SNL-WaterPower/siweed/documentation/diagrams/NoiseHistogram.pdf

-6 | -4 | -2 | 0 | 2 | 4 | 6 | 8
Torque Measured(N-m) | #10⁻⁵

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
Occurences
