SNL-WaterPower/siweed/documentation/diagrams/siweed_photo_with_callouts.pdf

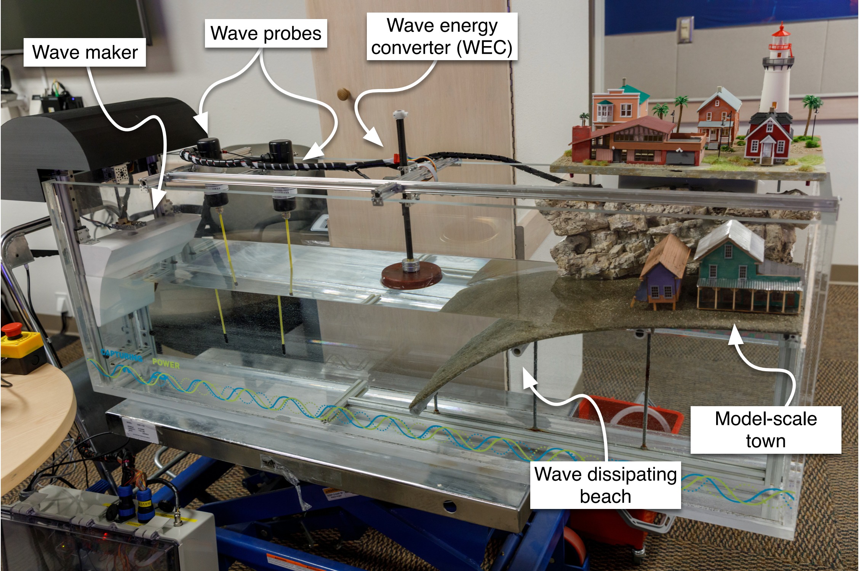
[picture p4: page 1]

Wave probes
Wave maker

Wave energy
converter (WEC)

Wave dissipating
beach

Model-scale
town
