SNL-WaterPower/siweed/Processing/siWeedGUI/1.png

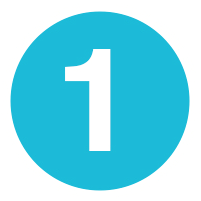
Processing/siWeedGUI/1.png
