SNL-WaterPower/siweed/Processing/siWeedGUI/2.png

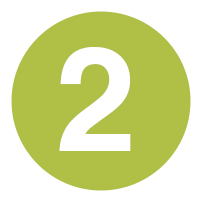
Processing/siWeedGUI/2.png
