SNL-WaterPower/siweed/documentation/SOLIDWORKS Town/Wave Maker (all parts)/FinalWaveMaker.SLDPRT

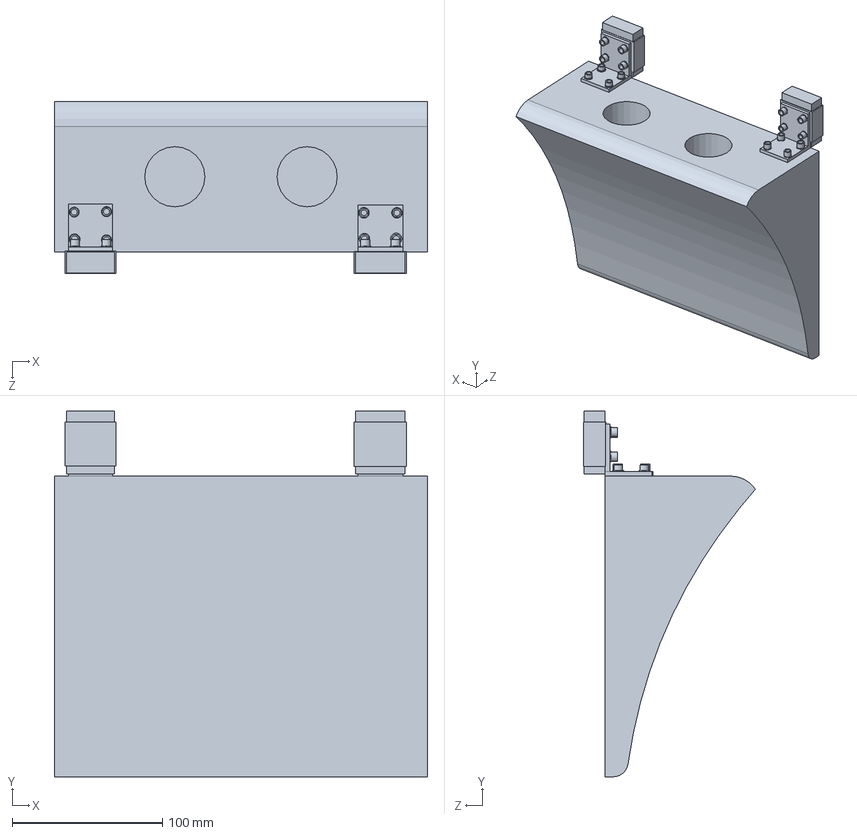
[picture p28: CAD file, 2022-12-22]
documentation/SOLIDWORKS Town/Wave Maker (all parts)/FinalWaveMaker.SLDPRT
248.0 x 243.1 x 114.3 mm
