SNL-WaterPower/siweed/documentation/SOLIDWORKS Town/Buoy (all prts)/Final buoy.SLDPRT

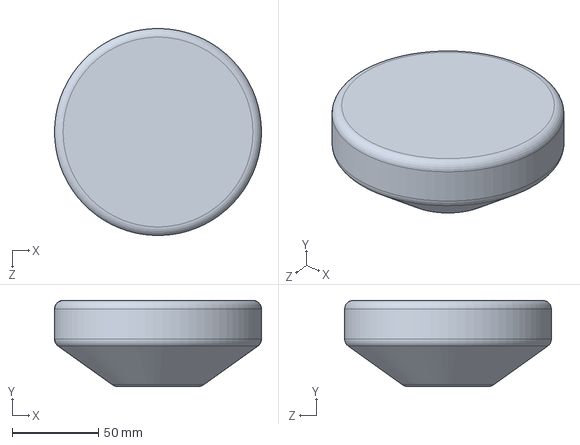
[picture p29: CAD file, 2022-12-22]
documentation/SOLIDWORKS Town/Buoy (all prts)/Final buoy.SLDPRT
120.0 x 50.0 x 119.9 mm
