SNL-WaterPower/siweed/documentation/SOLIDWORKS Town/Buildings/Beginner House.SLDPRT

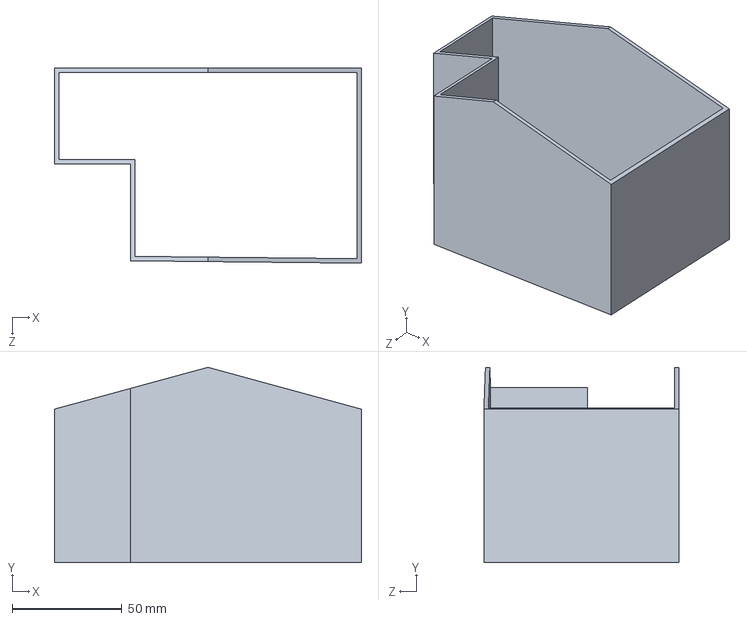
[picture p30: CAD file, 2022-12-22]
documentation/SOLIDWORKS Town/Buildings/Beginner House.SLDPRT
139.7 x 88.9 x 88.9 mm
