SNL-WaterPower/siweed/documentation/SOLIDWORKS Town/Buoy (all prts)/buoy.SLDPRT

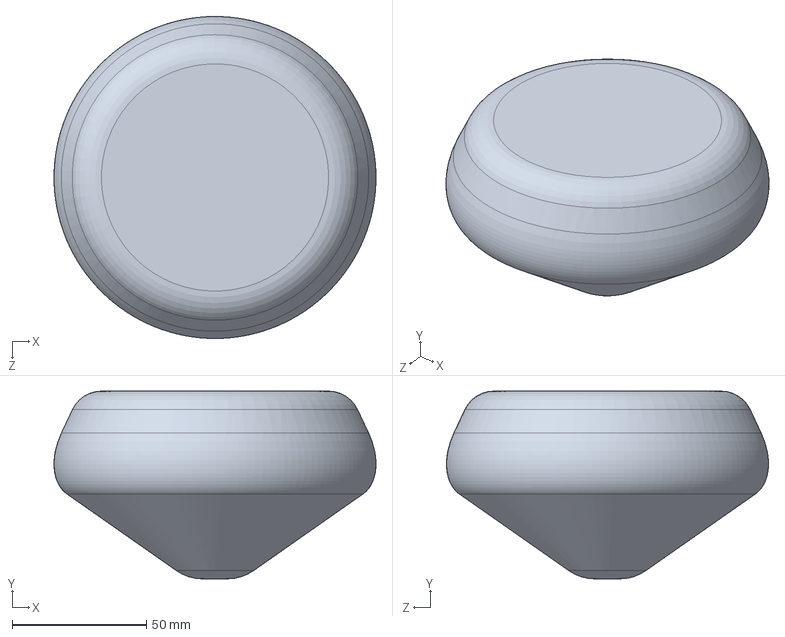
[picture p31: CAD file, 2022-12-22]
documentation/SOLIDWORKS Town/Buoy (all prts)/buoy.SLDPRT
120.0 x 70.0 x 120.0 mm
