SNL-WaterPower/siweed/documentation/SOLIDWORKS Town/Wave Maker (all parts)/Top Rods.SLDPRT

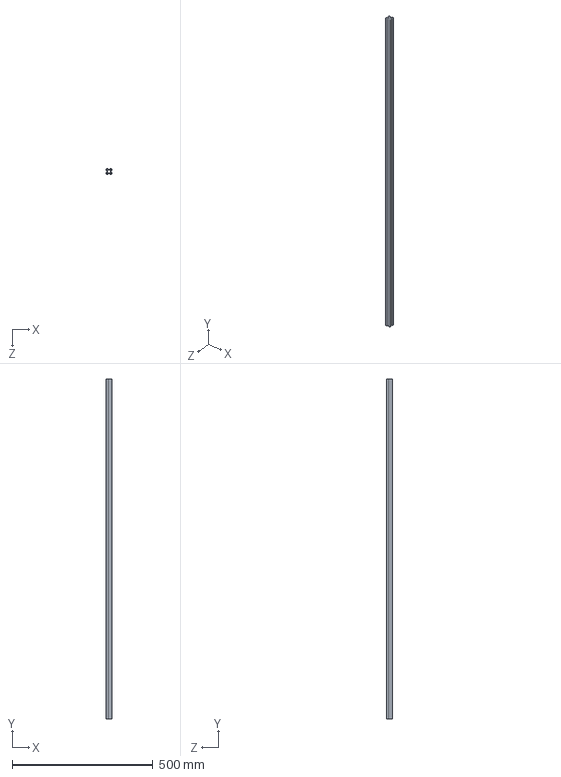
[picture p32: CAD file, 2022-12-22]
documentation/SOLIDWORKS Town/Wave Maker (all parts)/Top Rods.SLDPRT
20.1 x 1208.0 x 20.1 mm
