SNL-WaterPower/siweed/documentation/SOLIDWORKS Town/Buildings/light house.SLDPRT

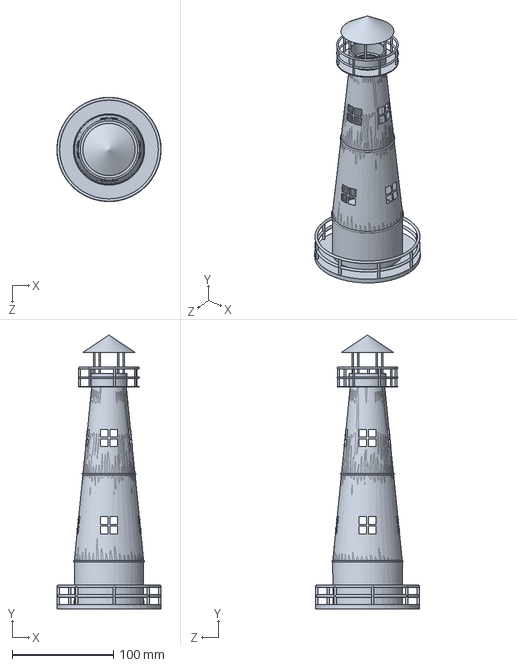
[picture p33: CAD file, 2022-12-22]
documentation/SOLIDWORKS Town/Buildings/light house.SLDPRT
103.0 x 270.3 x 103.0 mm
