SNL-WaterPower/siweed/documentation/SOLIDWORKS Town/Buoy (all prts)/Encoder.SLDPRT

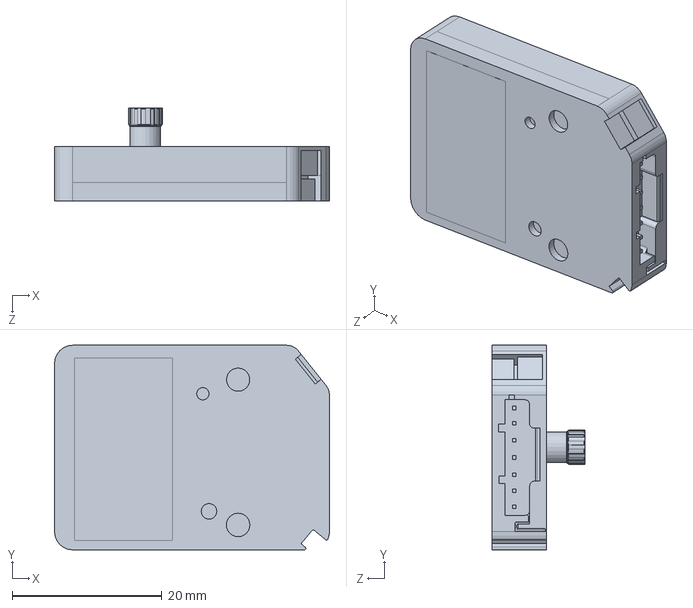
[picture p34: CAD file, 2022-12-22]
documentation/SOLIDWORKS Town/Buoy (all prts)/Encoder.SLDPRT
36.8 x 27.4 x 12.5 mm
