SNL-WaterPower/siweed/documentation/SOLIDWORKS Town/Wave Maker (all parts)/double S Top Rods -  - Copy.SLDPRT

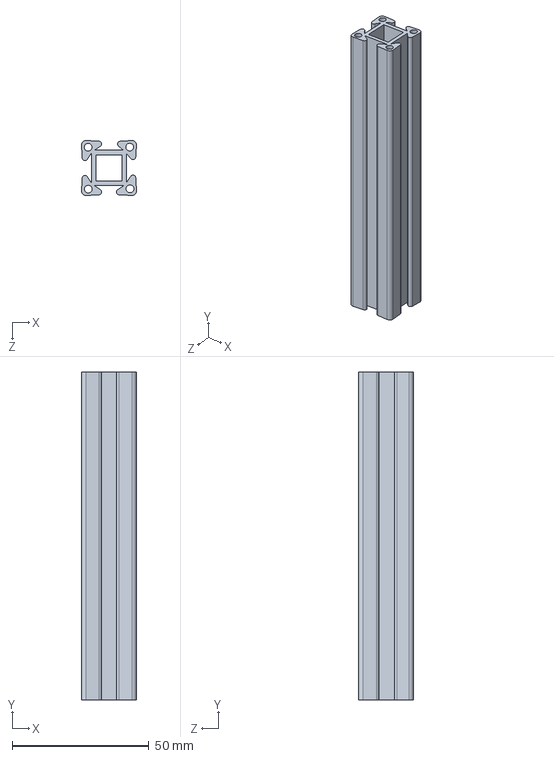
[picture p35: CAD file, 2022-12-22]
documentation/SOLIDWORKS Town/Wave Maker (all parts)/double S Top Rods - - Copy.SLDPRT
20.1 x 120.0 x 20.1 mm
