SNL-WaterPower/siweed/documentation/SOLIDWORKS Town/Buildings/beach shack.SLDPRT

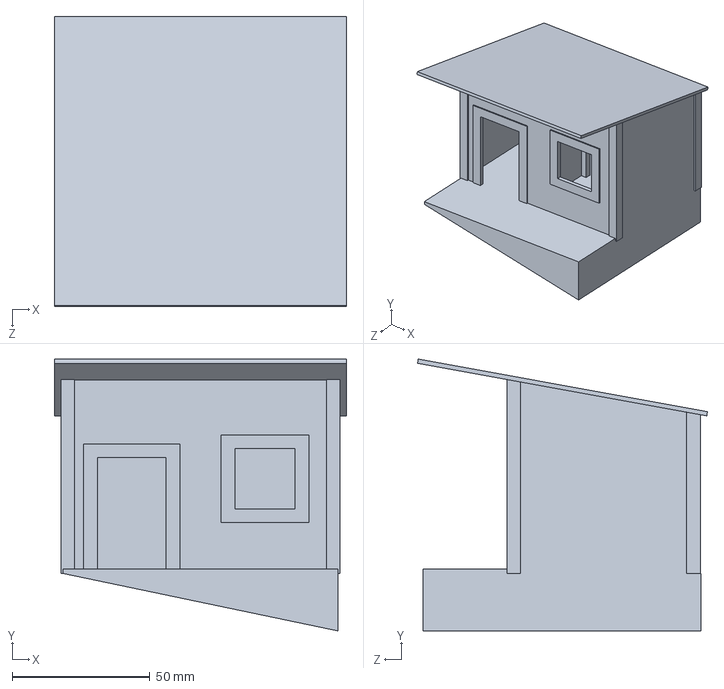
[picture p36: CAD file, 2022-12-22]
documentation/SOLIDWORKS Town/Buildings/beach shack.SLDPRT
106.2 x 98.8 x 105.4 mm
