SNL-WaterPower/siweed/documentation/SOLIDWORKS Town/Wave Maker (all parts)/mini bracket.SLDPRT

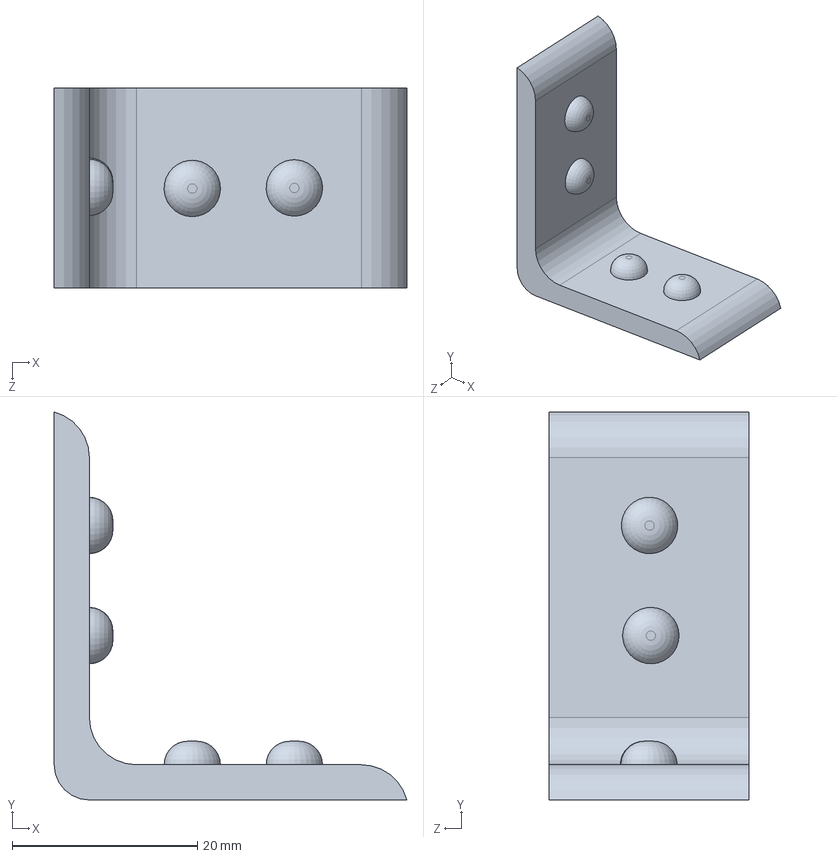
[picture p37: CAD file, 2022-12-22]
documentation/SOLIDWORKS Town/Wave Maker (all parts)/mini bracket.SLDPRT
38.1 x 41.9 x 21.6 mm
