SNL-WaterPower/siweed/documentation/SOLIDWORKS Town/Buildings/House.SLDPRT

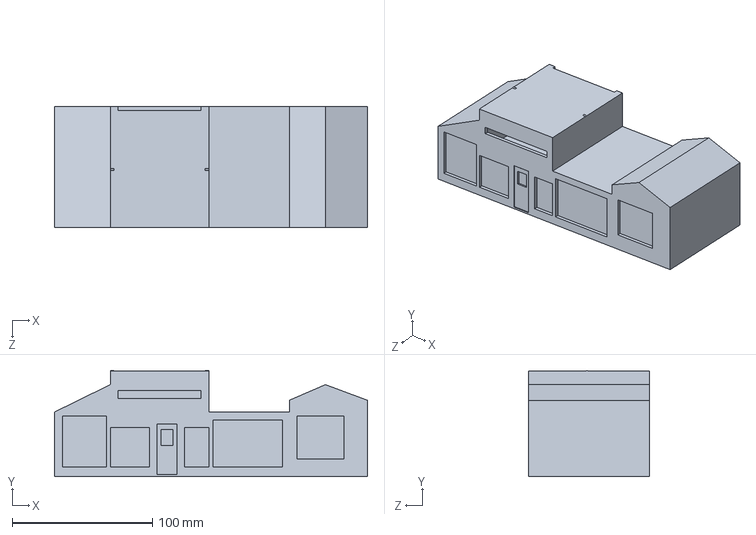
[picture p38: CAD file, 2022-12-22]
documentation/SOLIDWORKS Town/Buildings/House.SLDPRT
223.5 x 75.8 x 86.1 mm
