SNL-WaterPower/siweed/documentation/SOLIDWORKS Town/Wave Maker (all parts)/Horiz Rod.SLDPRT

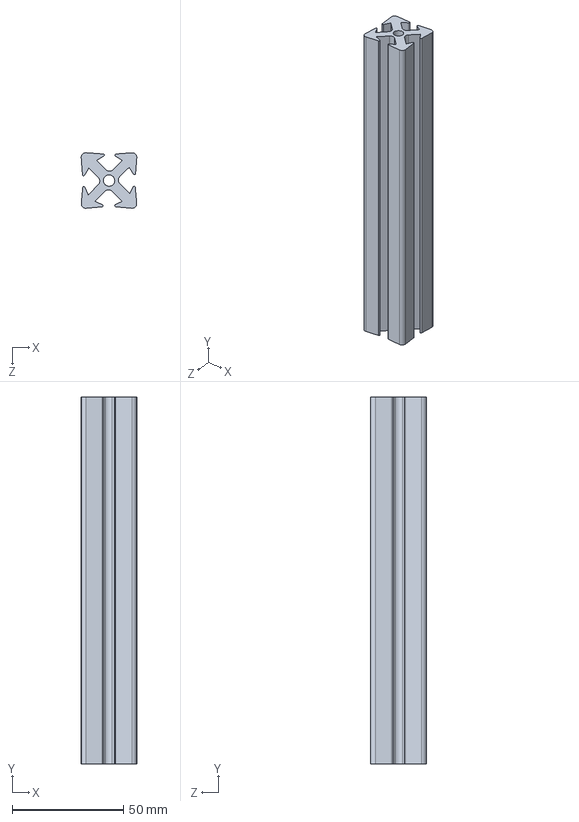
[picture p39: CAD file, 2022-12-22]
documentation/SOLIDWORKS Town/Wave Maker (all parts)/Horiz Rod.SLDPRT
25.0 x 165.2 x 25.0 mm
