SNL-WaterPower/siweed/documentation/SOLIDWORKS Town/Buoy (all prts)/bracket.SLDPRT

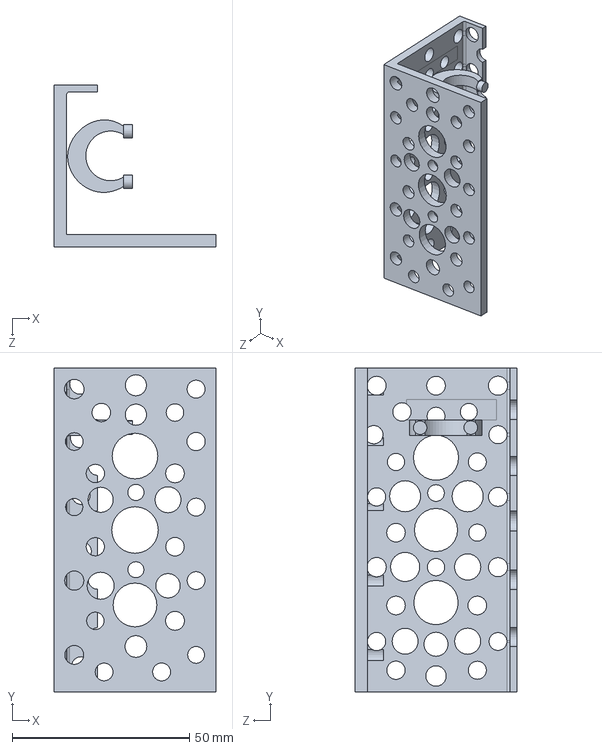
[picture p40: CAD file, 2022-12-22]
documentation/SOLIDWORKS Town/Buoy (all prts)/bracket.SLDPRT
45.7 x 91.4 x 45.7 mm
