SNL-WaterPower/siweed/documentation/SOLIDWORKS Town/Wave Maker (all parts)/Pulley.SLDPRT

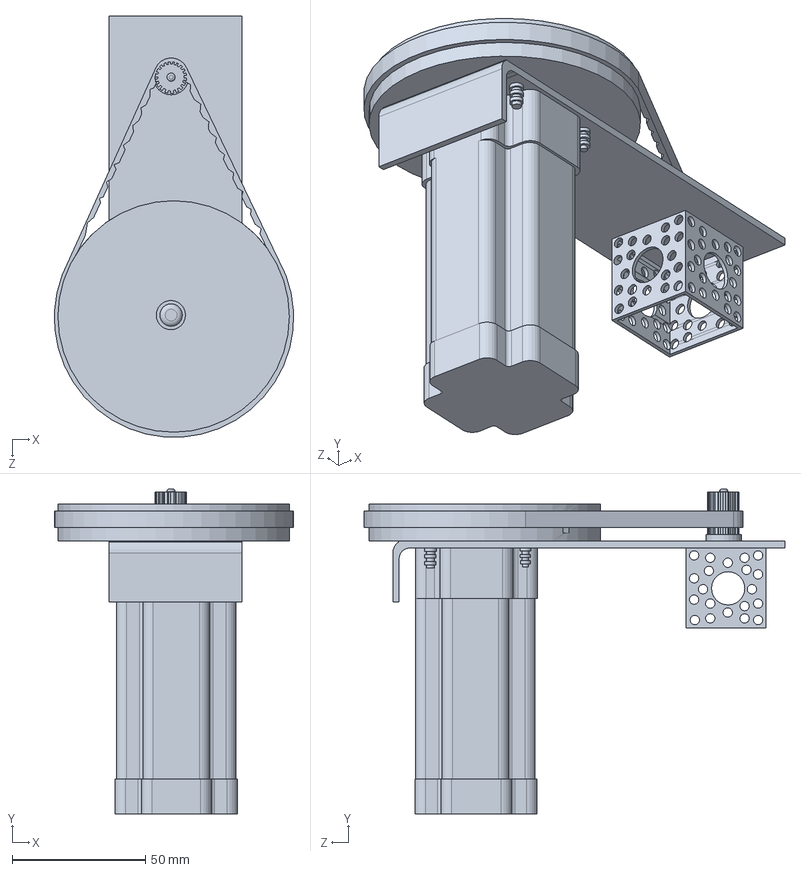
[picture p41: CAD file, 2022-12-22]
documentation/SOLIDWORKS Town/Wave Maker (all parts)/Pulley.SLDPRT
89.9 x 122.2 x 158.3 mm
