SNL-WaterPower/siweed/documentation/SOLIDWORKS Town/Buoy (all prts)/Motor.SLDPRT

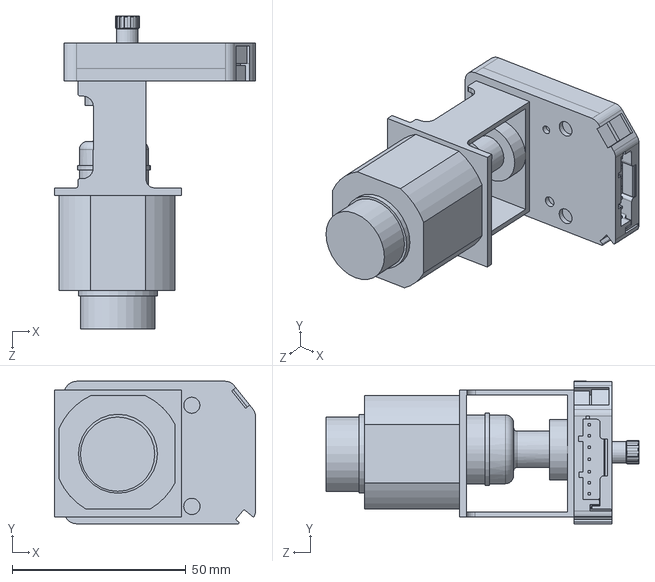
[picture p42: CAD file, 2022-12-22]
documentation/SOLIDWORKS Town/Buoy (all prts)/Motor.SLDPRT
57.9 x 41.1 x 90.0 mm
