SNL-WaterPower/siweed/documentation/SOLIDWORKS Town/Wave Maker (all parts)/Rod.SLDPRT

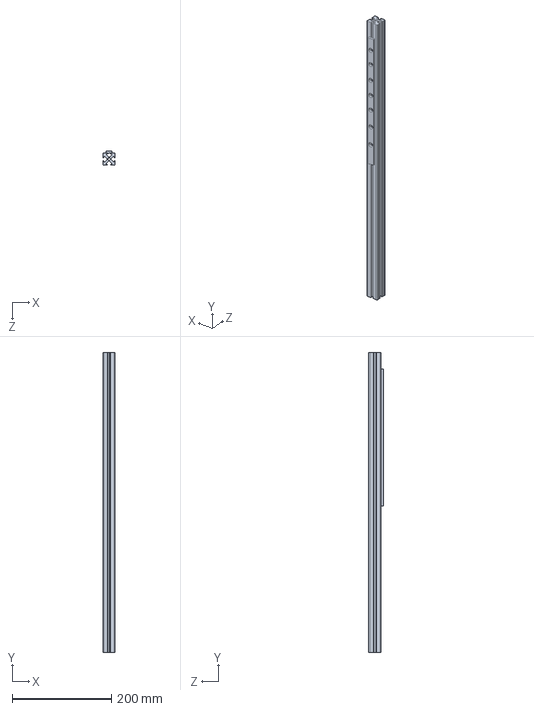
[picture p43: CAD file, 2022-12-22]
documentation/SOLIDWORKS Town/Wave Maker (all parts)/Rod.SLDPRT
25.0 x 603.2 x 29.3 mm
