SNL-WaterPower/siweed/documentation/SOLIDWORKS Town/Wave Maker (all parts)/U Bracket.SLDPRT

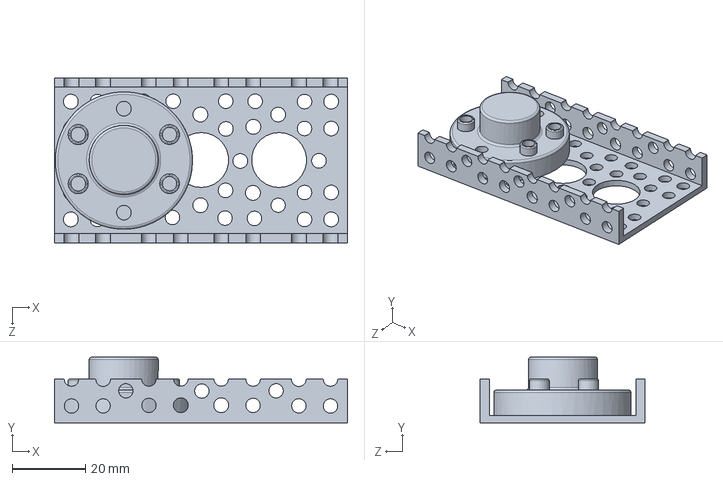
[picture p44: CAD file, 2022-12-22]
documentation/SOLIDWORKS Town/Wave Maker (all parts)/U Bracket.SLDPRT
80.0 x 18.0 x 45.0 mm
