SNL-WaterPower/siweed/documentation/SOLIDWORKS Town/Wave Maker (all parts)/rod connector.SLDPRT

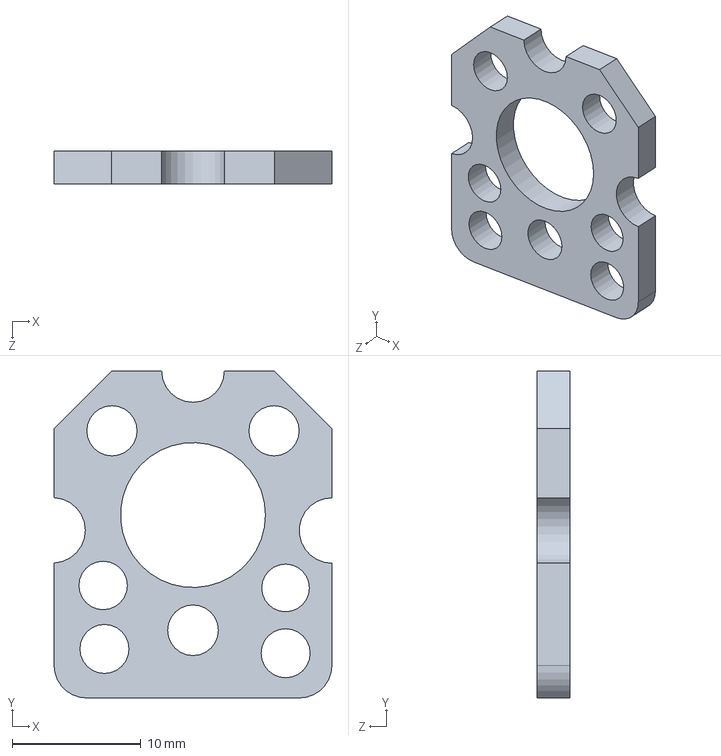
[picture p45: CAD file, 2022-12-22]
documentation/SOLIDWORKS Town/Wave Maker (all parts)/rod connector.SLDPRT
21.6 x 25.4 x 2.54 mm
