SNL-WaterPower/siweed/documentation/diagrams/TorqueCommanded.pdf

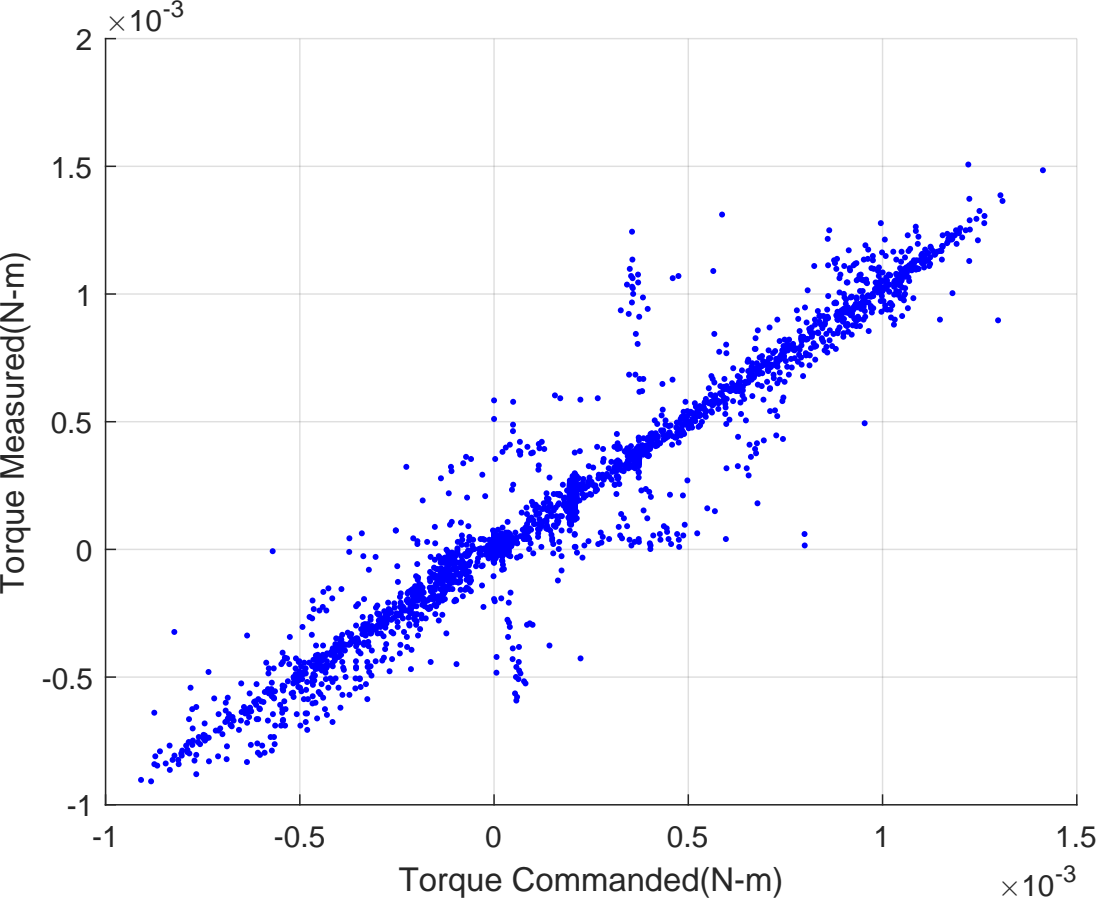
[picture p54: page 1]
Torque Commanded(N-m); Torque Measured(N-m)
