SNL-WaterPower/siweed/documentation/diagrams/TorqueConstant.pdf

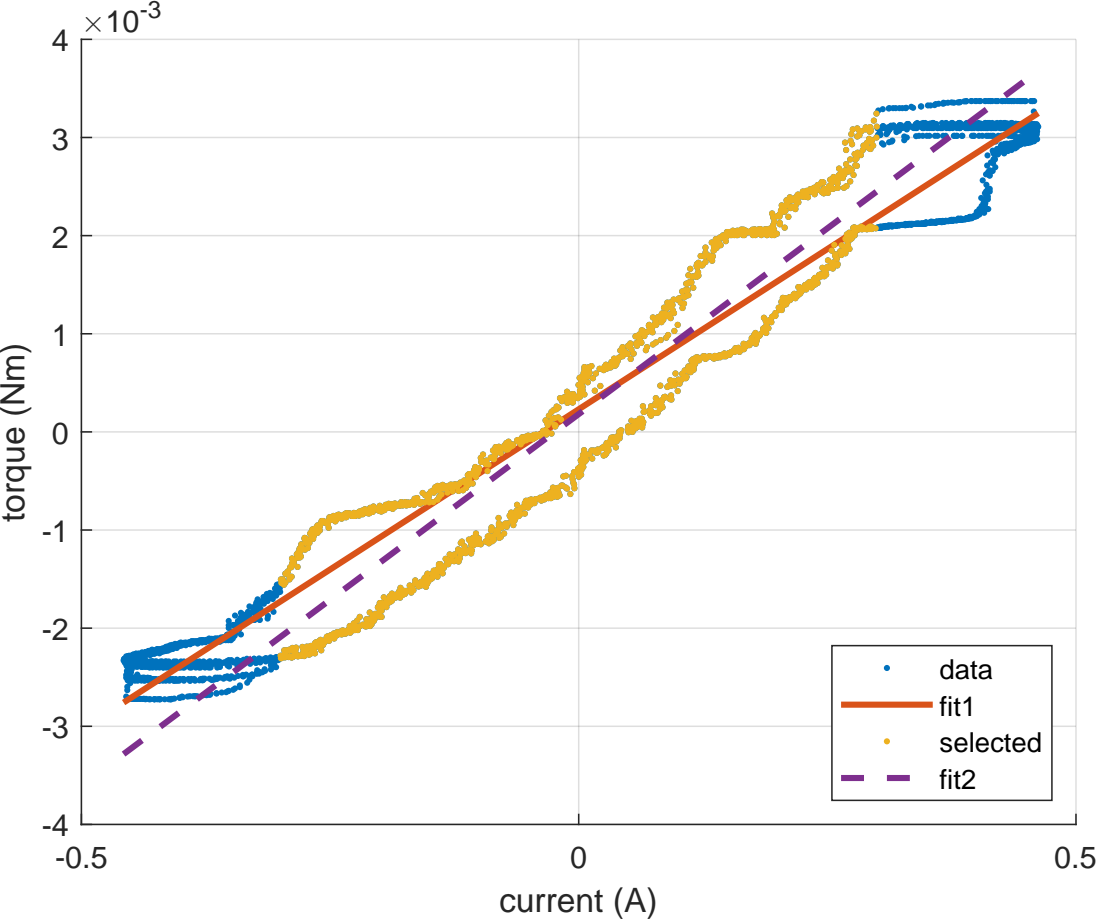
[picture p55: page 1]
current (A); torque (Nm); data fit1 selected fit2
